Armandpl/furuta/robot/hardware/v1/m10_weight.stl

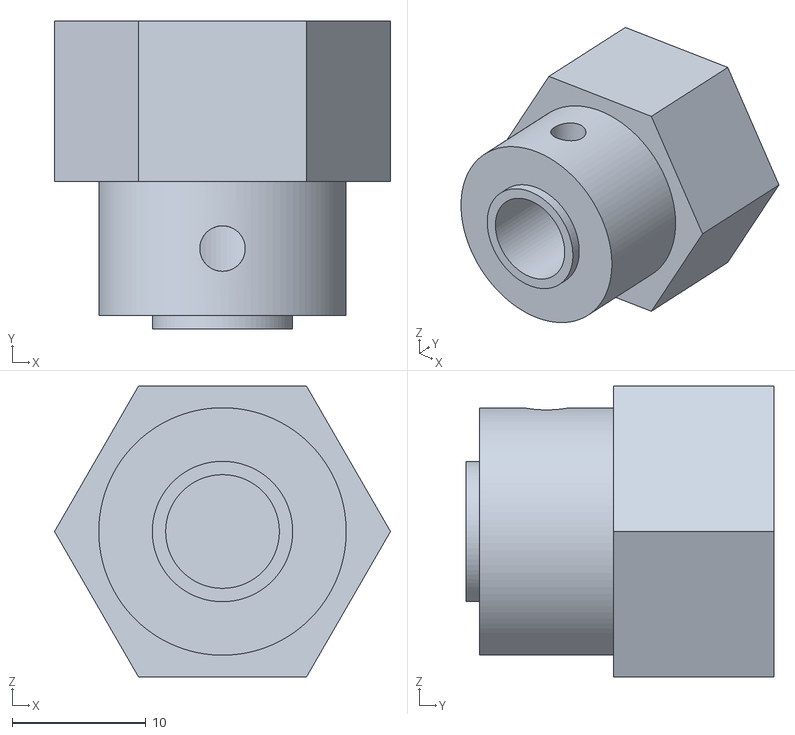
[picture p16: CAD file, 2022-12-12, an earlier design]
robot/hardware/v1/m10_weight.stl
25.1 x 23.0 x 21.8
